mrg-mex/Proyecto_1_robotica_sem_2023-1/Entrega/Case PCA Final/BasePCA.SLDPRT

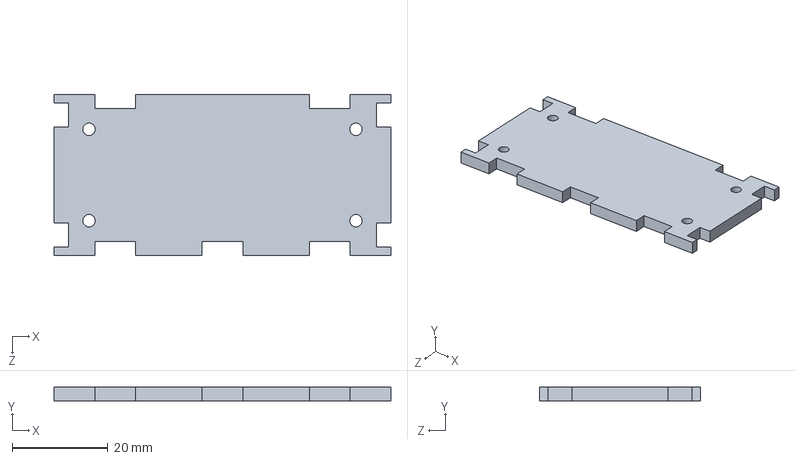
[picture p29: CAD file, 2023-01-16]
Entrega/Case PCA Final/BasePCA.SLDPRT
70.2 x 3.00 x 33.7 mm
