mrg-mex/Proyecto_1_robotica_sem_2023-1/Archivos_referencia/gripper_palm_to_finger_large.stl

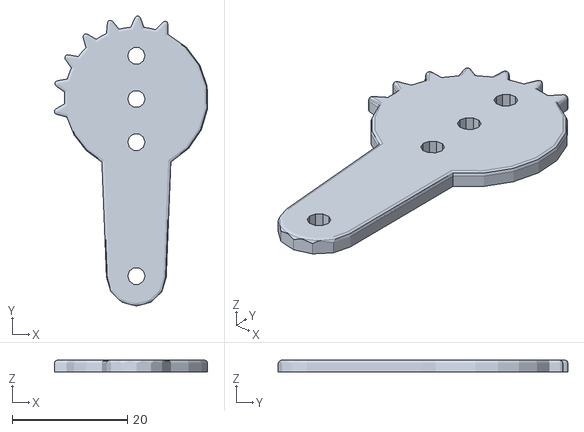
[picture p31: CAD file, 2022-12-05]
Archivos_referencia/gripper_palm_to_finger_large.stl
26.6 x 50.4 x 2.00
