mrg-mex/Proyecto_1_robotica_sem_2023-1/Entrega/Case PCA Final/LateralIzqPCA.SLDPRT

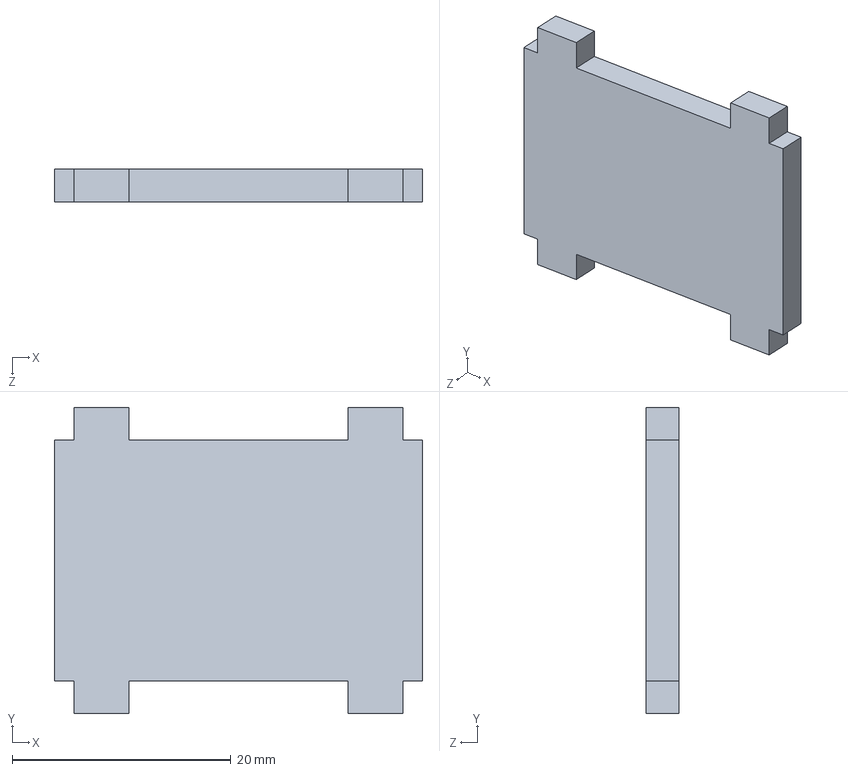
[picture p32: CAD file, 2023-01-16]
Entrega/Case PCA Final/LateralIzqPCA.SLDPRT
33.7 x 28.0 x 3.00 mm
