mrg-mex/Proyecto_1_robotica_sem_2023-1/Entrega/Case Raspberry Final/Part3.SLDPRT

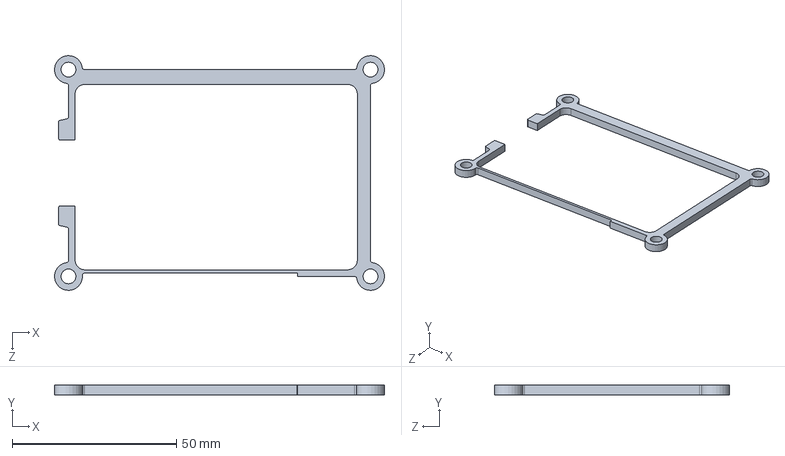
[picture p33: CAD file, 2023-01-16]
Entrega/Case Raspberry Final/Part3.SLDPRT
100.5 x 3.00 x 71.5 mm
