mrg-mex/Proyecto_1_robotica_sem_2023-1/Archivos_referencia/gripper_l_bracket.stl

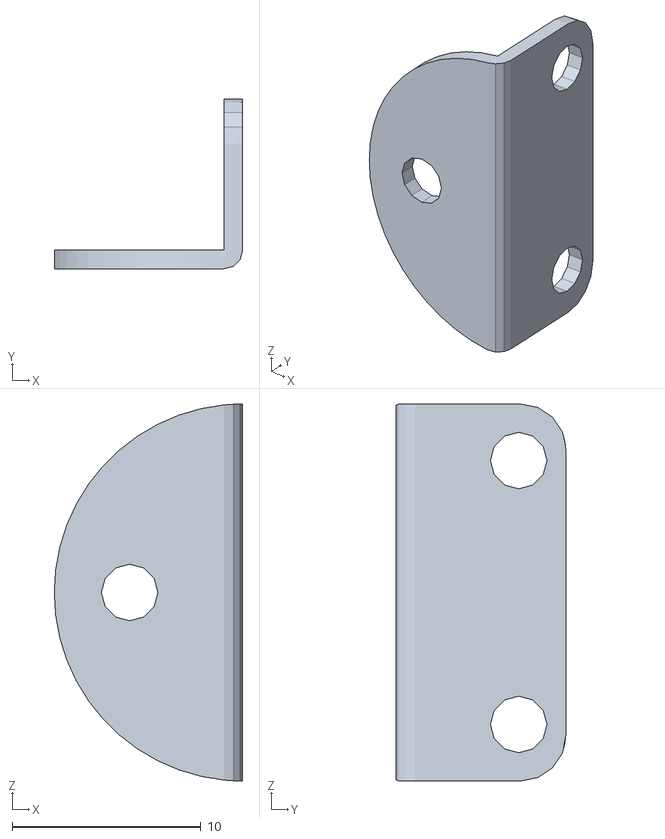
[picture p34: CAD file, 2022-12-05]
Archivos_referencia/gripper_l_bracket.stl
10.00 x 9.00 x 20.0
