mrg-mex/Proyecto_1_robotica_sem_2023-1/Archivos_referencia/miniature_ball_radial_bearing.stl

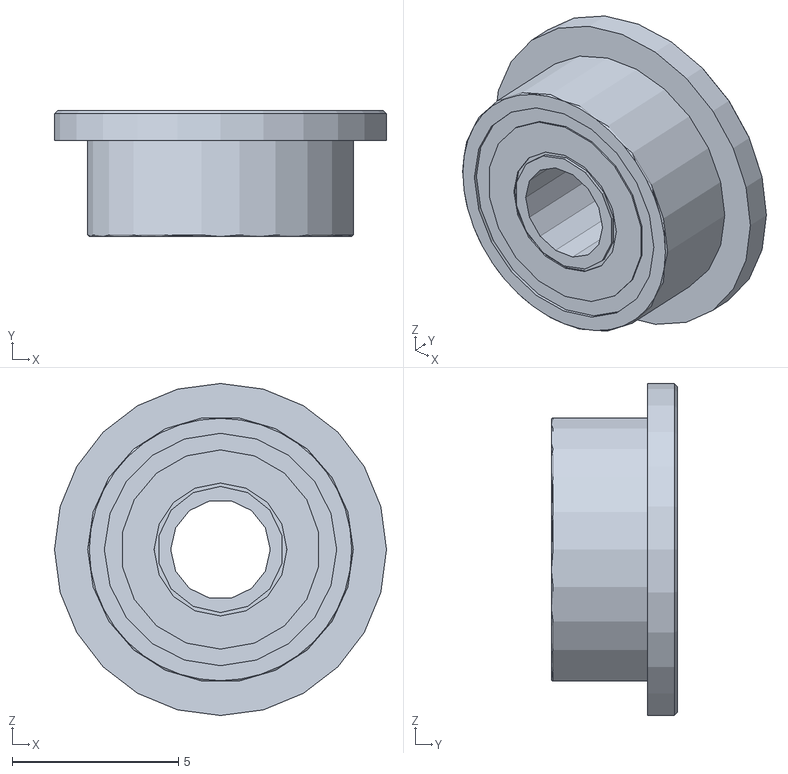
[picture p37: CAD file, 2022-12-05]
Archivos_referencia/miniature_ball_radial_bearing.stl
10.0 x 3.80 x 10.0
