mrg-mex/Proyecto_1_robotica_sem_2023-1/Archivos_referencia/finger.stl

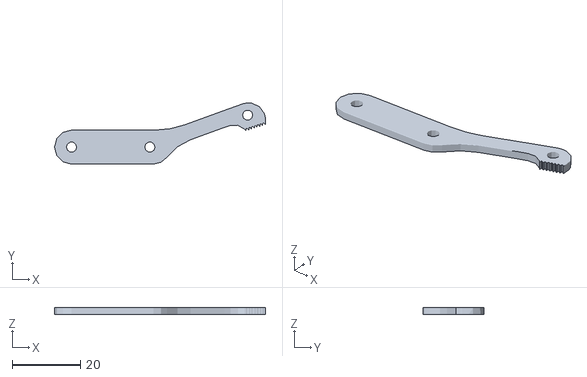
[picture p38: CAD file, 2022-12-05]
Archivos_referencia/finger.stl
61.9 x 18.0 x 2.00
