mrg-mex/Proyecto_1_robotica_sem_2023-1/Entrega/Case Raspberry Final/Pt9.SLDPRT

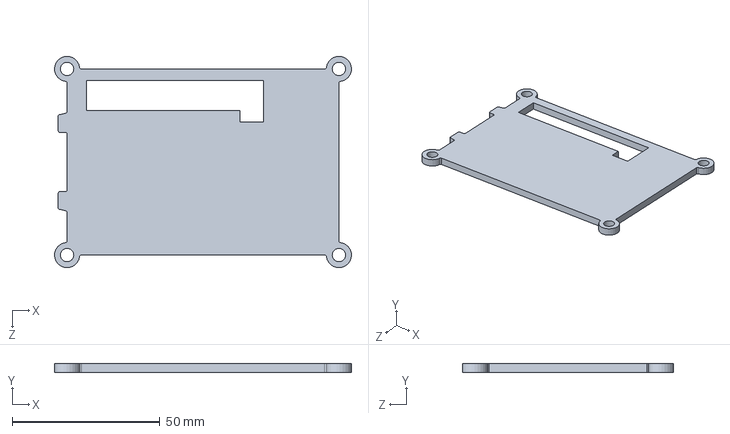
[picture p39: CAD file, 2023-01-16]
Entrega/Case Raspberry Final/Pt9.SLDPRT
100.5 x 3.00 x 71.5 mm
