mrg-mex/Proyecto_1_robotica_sem_2023-1/Archivos_referencia/u_type_robot_waist_bracket.stl

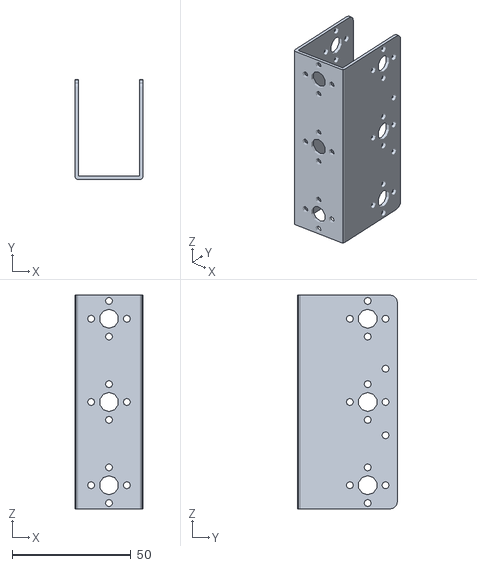
[picture p40: CAD file, 2022-12-05]
Archivos_referencia/u_type_robot_waist_bracket.stl
28.5 x 42.0 x 90.0
