mrg-mex/Proyecto_1_robotica_sem_2023-1/Archivos_referencia/spacer_short.stl

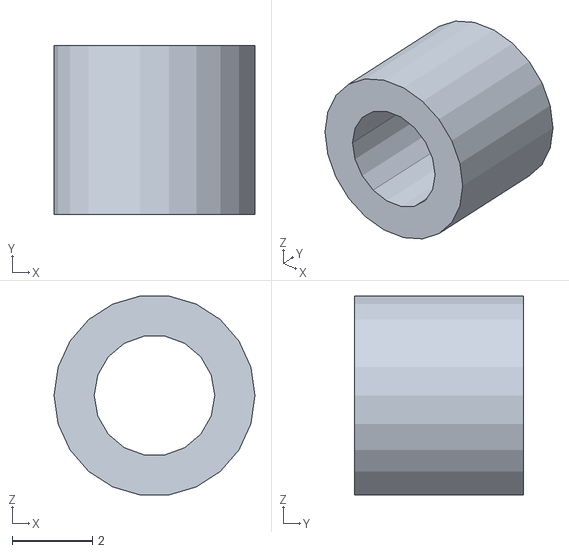
[picture p41: CAD file, 2022-12-05]
Archivos_referencia/spacer_short.stl
5.00 x 4.20 x 4.95
