mrg-mex/Proyecto_1_robotica_sem_2023-1/Archivos_referencia/long_u_type_servo_bracket.stl

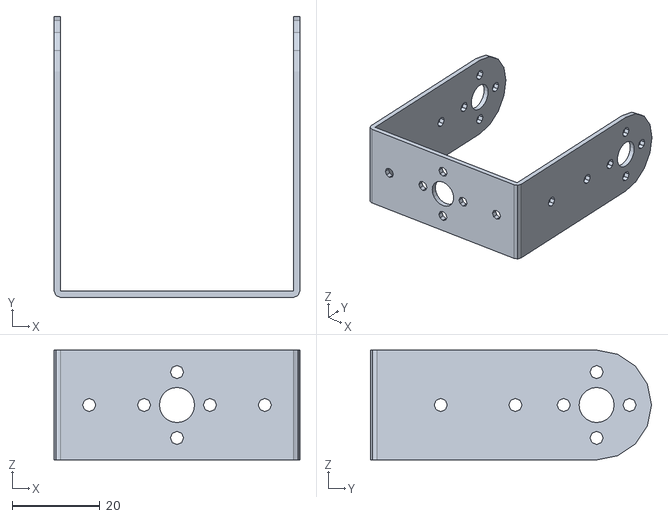
[picture p42: CAD file, 2022-12-05]
Archivos_referencia/long_u_type_servo_bracket.stl
56.0 x 64.0 x 25.0
