mrg-mex/Proyecto_1_robotica_sem_2023-1/Archivos_referencia/aluminum_servo_horn.stl

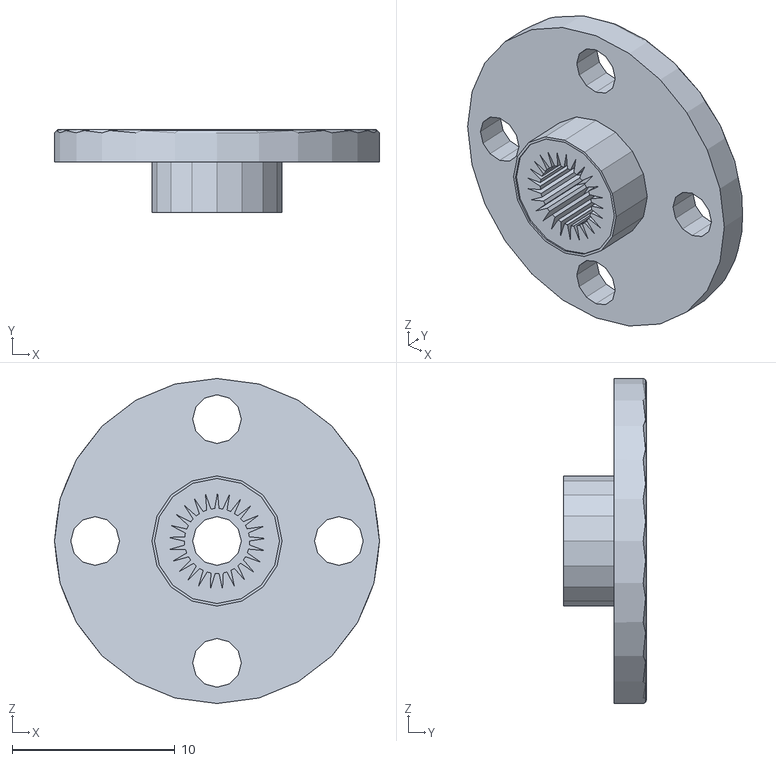
[picture p43: CAD file, 2022-12-05]
Archivos_referencia/aluminum_servo_horn.stl
20.0 x 5.10 x 20.0
