mrg-mex/Proyecto_1_robotica_sem_2023-1/Archivos_referencia/mg996r_servo.stl

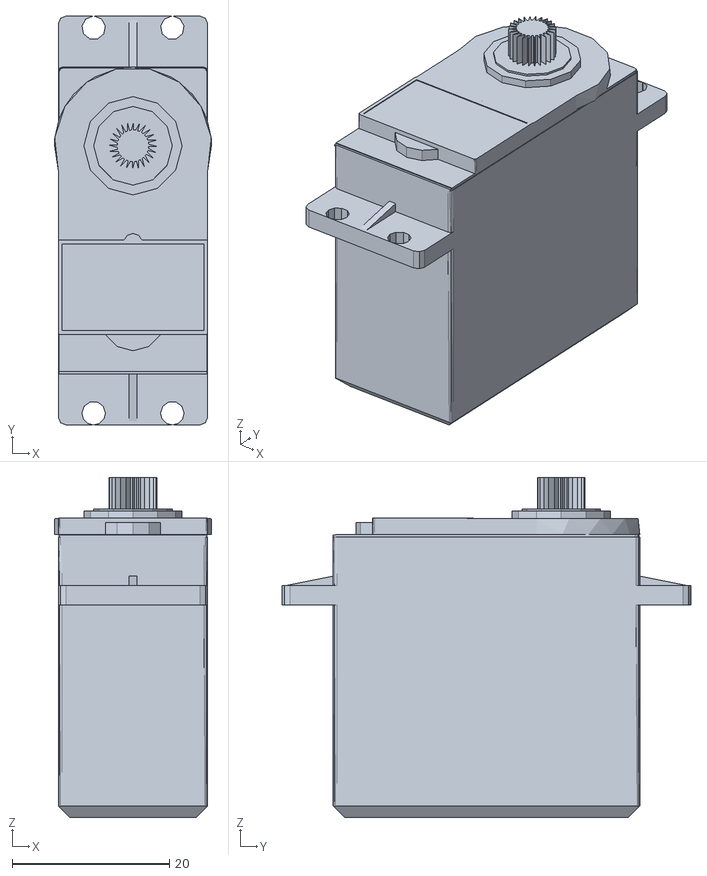
[picture p44: CAD file, 2022-12-05]
Archivos_referencia/mg996r_servo.stl
20.0 x 52.0 x 43.2
