mrg-mex/Proyecto_1_robotica_sem_2023-1/Archivos_referencia/l_type_servo_bracket.stl

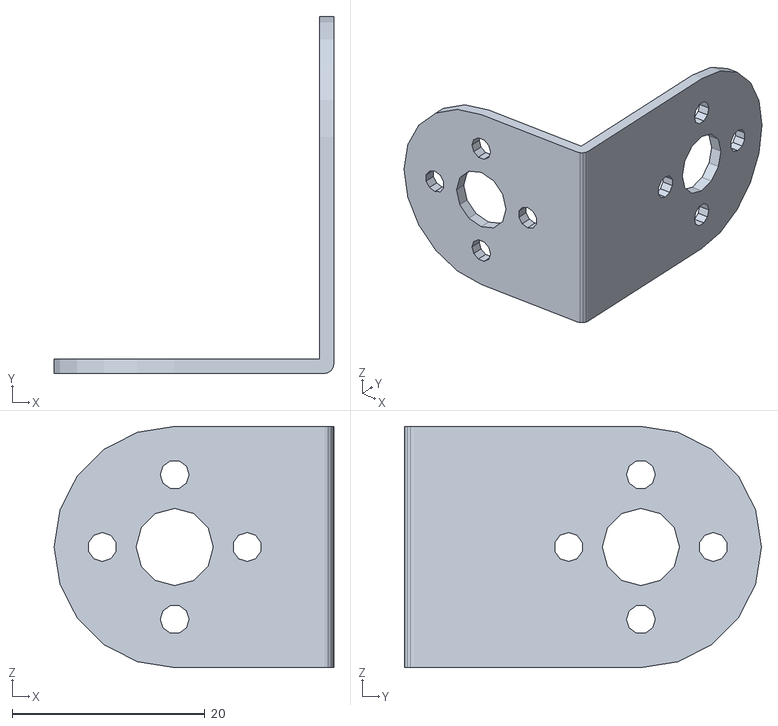
[picture p45: CAD file, 2022-12-05]
Archivos_referencia/l_type_servo_bracket.stl
29.0 x 37.0 x 25.0
